doruk6734/esp32-multisensory-alarm/media/photo_4.jpg

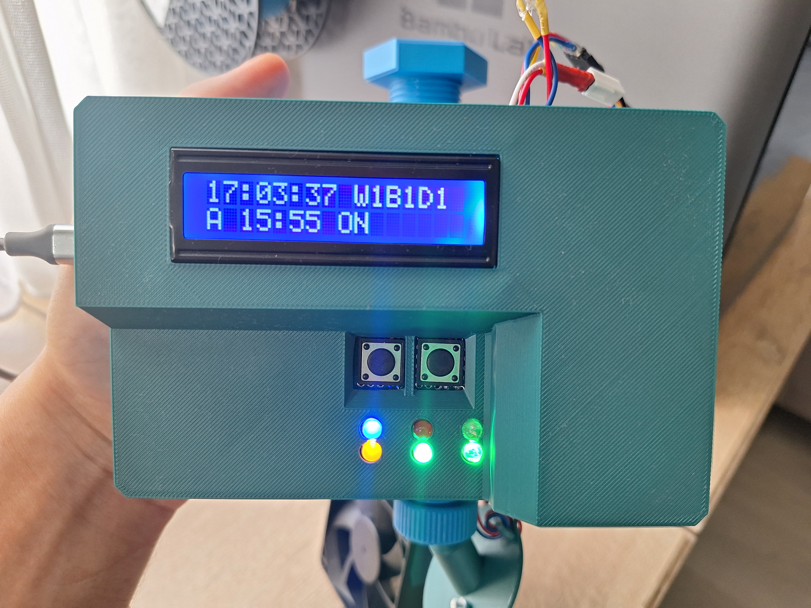
media/photo_4.jpg
